joshajohnson/stm32f103-feather/firmware/blinky/Inc/main.h

#define LED_nRED_Pin GPIO_PIN_13
#define LED_nRED_GPIO_Port GPIOB
#define LED_nGRN_Pin GPIO_PIN_14
#define LED_nGRN_GPIO_Port GPIOB
#define LED_nBLU_Pin GPIO_PIN_15
#define LED_nBLU_GPIO_Port GPIOB
#define LED_nUSR_Pin GPIO_PIN_8
#define LED_nUSR_GPIO_Port GPIOA
